MBkams/System_MCU/firmware/Stm32l04/Core/Inc/Serial.h

// Cette fonction pourra être utilisée par le Shell
unsigned char SerialTransmit(char * pData, unsigned short Size);

// Dans cet exemple, on fait du polling, et c'est pas très grave
void SerialReceiveChar(char * pData, unsigned short Size);
